WannSea/throttle/gashebel/1C23_powertrain_3D_models/2741400000.stp

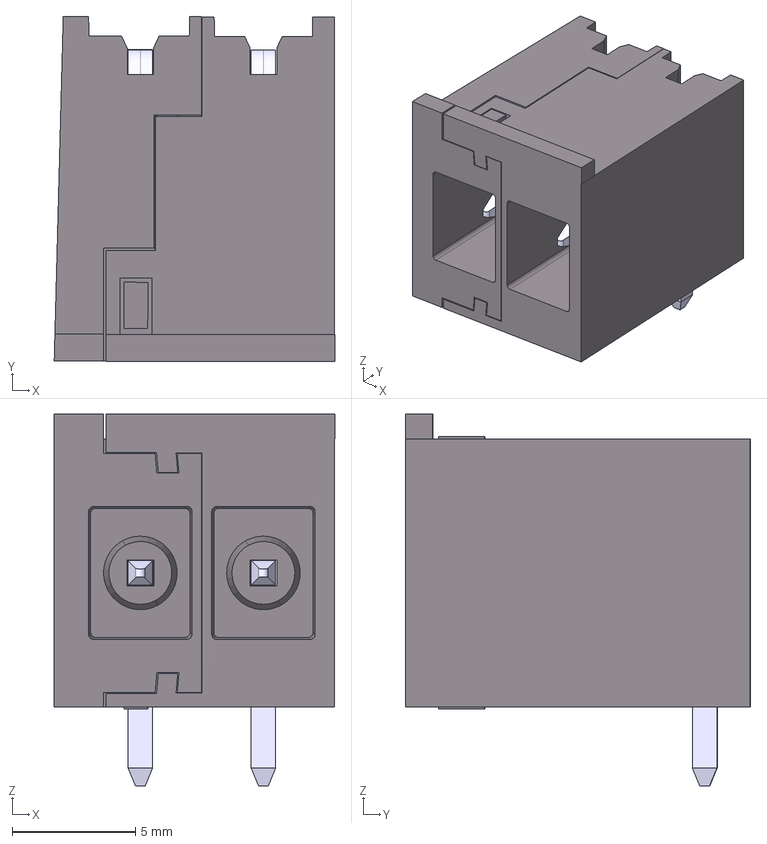
[picture p15: CAD file, 2025-12-10]
gashebel/1C23_powertrain_3D_models/2741400000.stp
11.4 x 14.0 x 15.1 mm
