WannSea/throttle/gashebel/1C23_powertrain_3D_models/705510038.stp

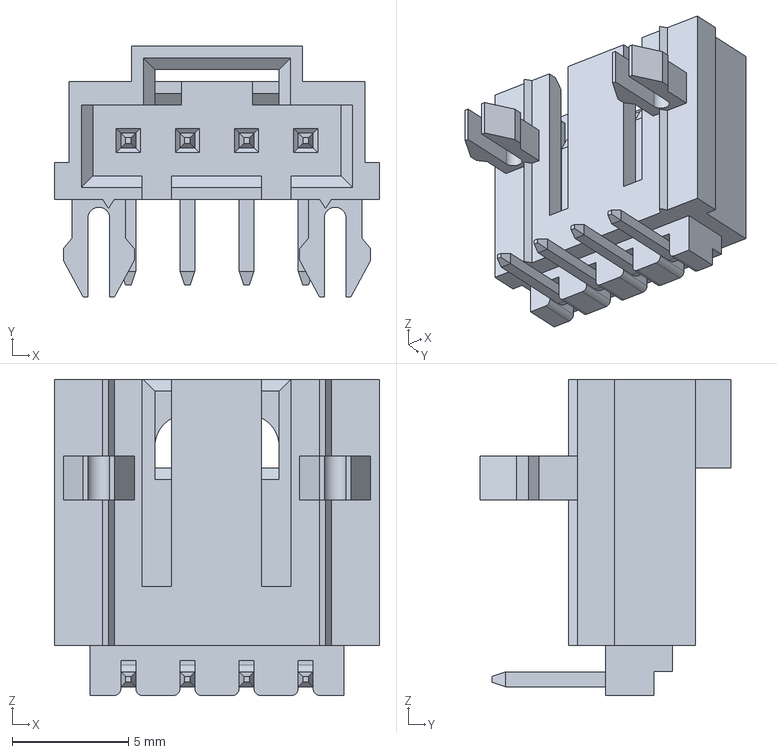
[picture p16: CAD file, 2025-12-10]
gashebel/1C23_powertrain_3D_models/705510038.stp
14.0 x 10.8 x 13.6 mm
