WannSea/throttle/gashebel/1C23_powertrain_3D_models/705510037.stp

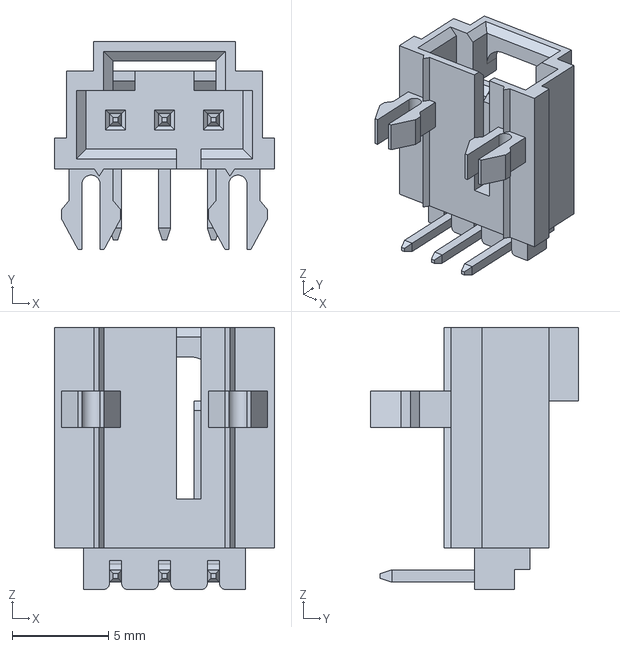
[picture p17: CAD file, 2025-12-10]
gashebel/1C23_powertrain_3D_models/705510037.stp
11.4 x 10.8 x 13.6 mm
