WannSea/throttle/gashebel/1C23_powertrain_3D_models/705510040.stp

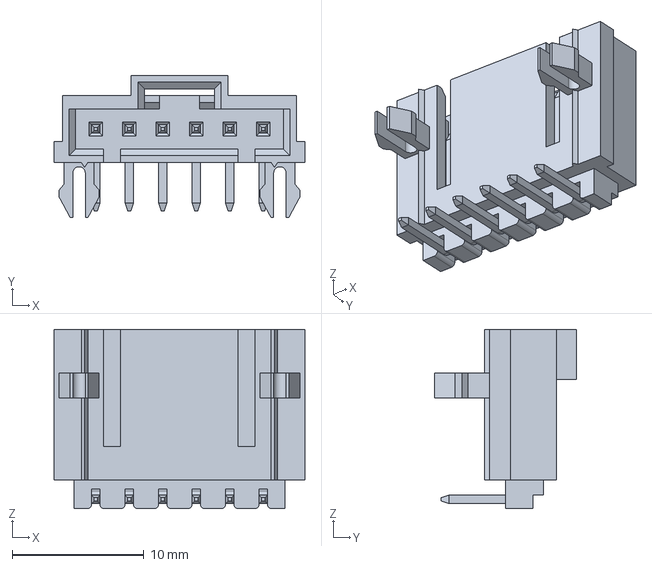
[picture p18: CAD file, 2025-12-10]
gashebel/1C23_powertrain_3D_models/705510040.stp
19.0 x 10.8 x 13.6 mm
